TRUNKSNEO/HomeLab-PDU-V1/Images/10in-Dual/10in-Dual-B.png

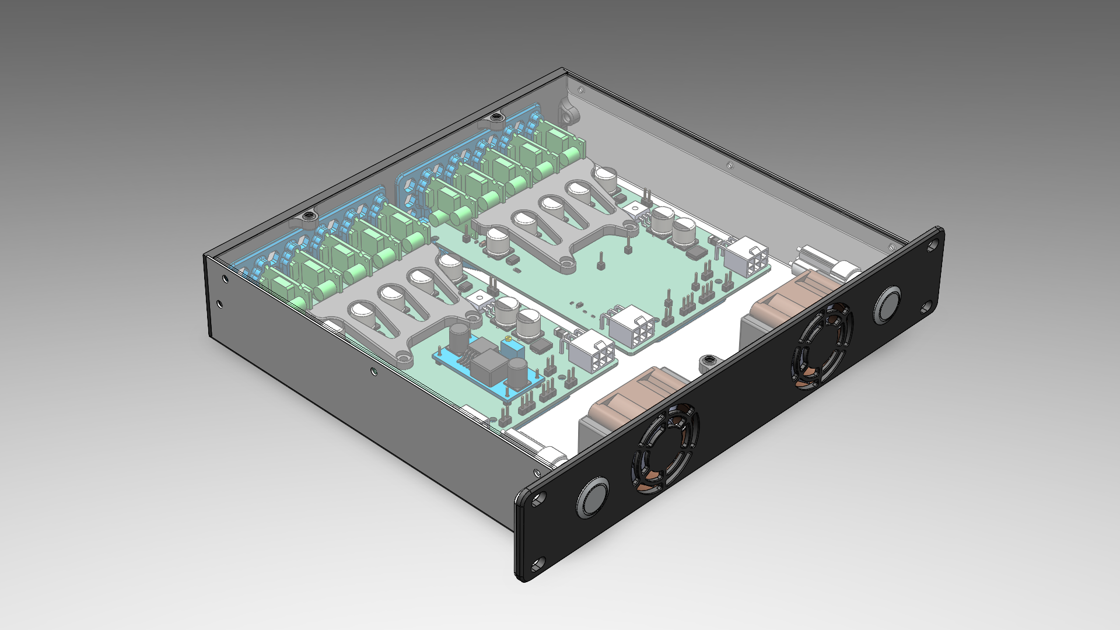
Images/10in-Dual/10in-Dual-B.png
