TRUNKSNEO/HomeLab-PDU-V1/Images/10in-Single/10in-Single-B.png

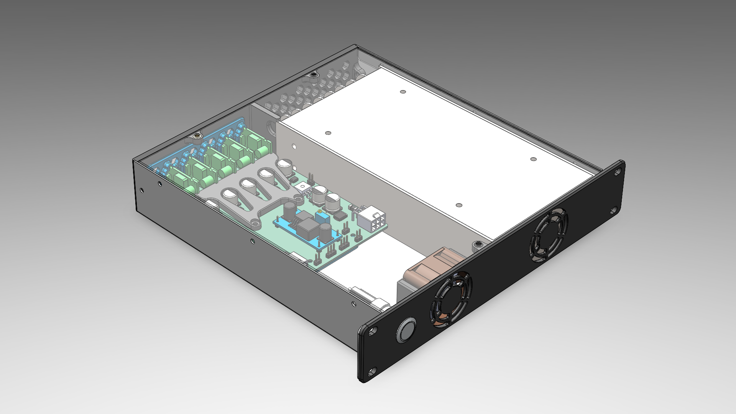
Images/10in-Single/10in-Single-B.png
