TRUNKSNEO/HomeLab-PDU-V1/Images/10in_3D_Modular/10in_3D_Modular-C.png

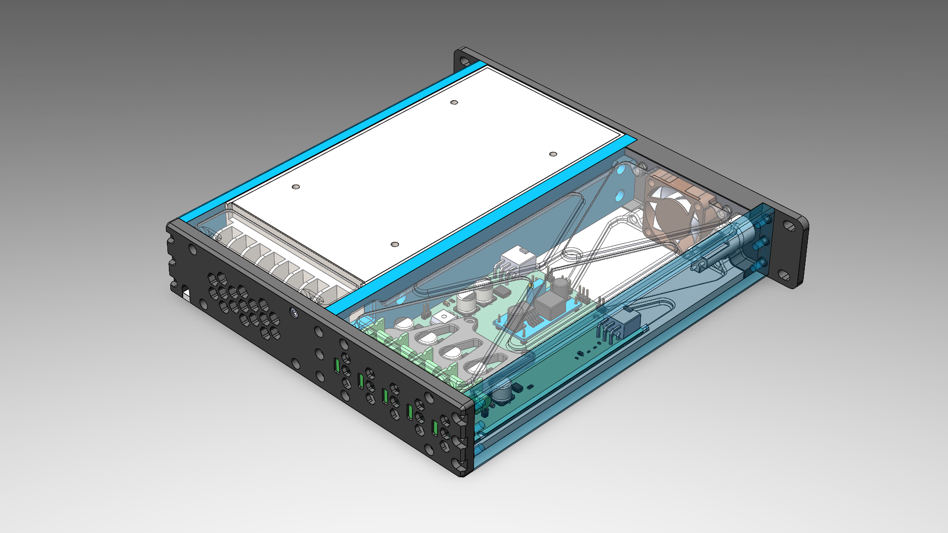
Images/10in_3D_Modular/10in_3D_Modular-C.png
