TRUNKSNEO/HomeLab-PDU-V1/Images/10in_3D_Unibody/10in_3D_Unibody-A.png

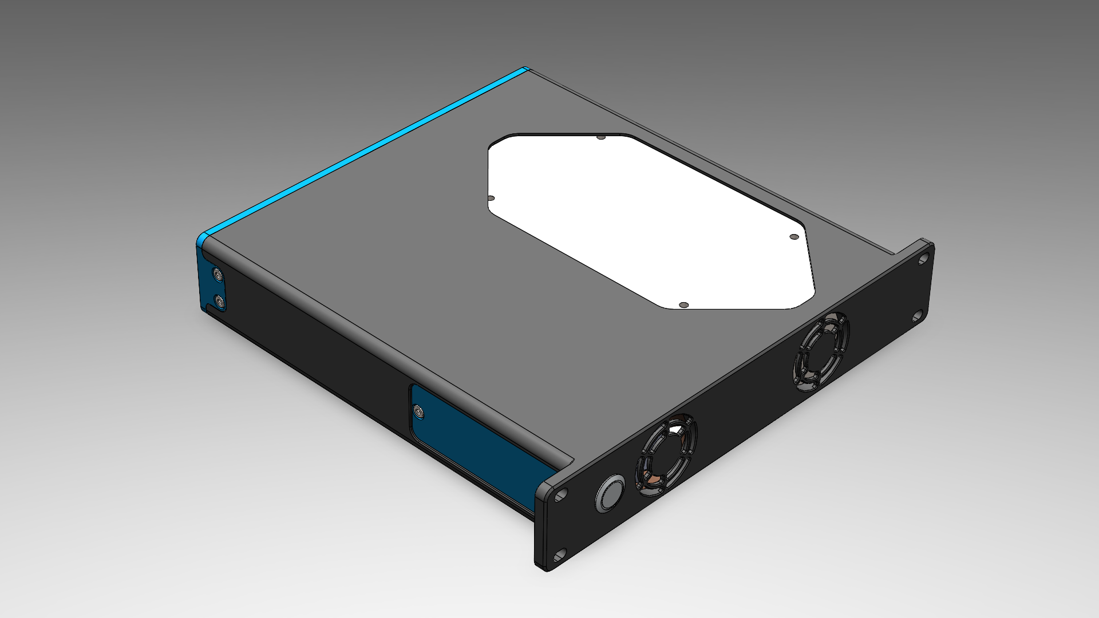
Images/10in_3D_Unibody/10in_3D_Unibody-A.png
