TRUNKSNEO/HomeLab-PDU-V1/Images/19in-Dual/19in-Dual-A.png

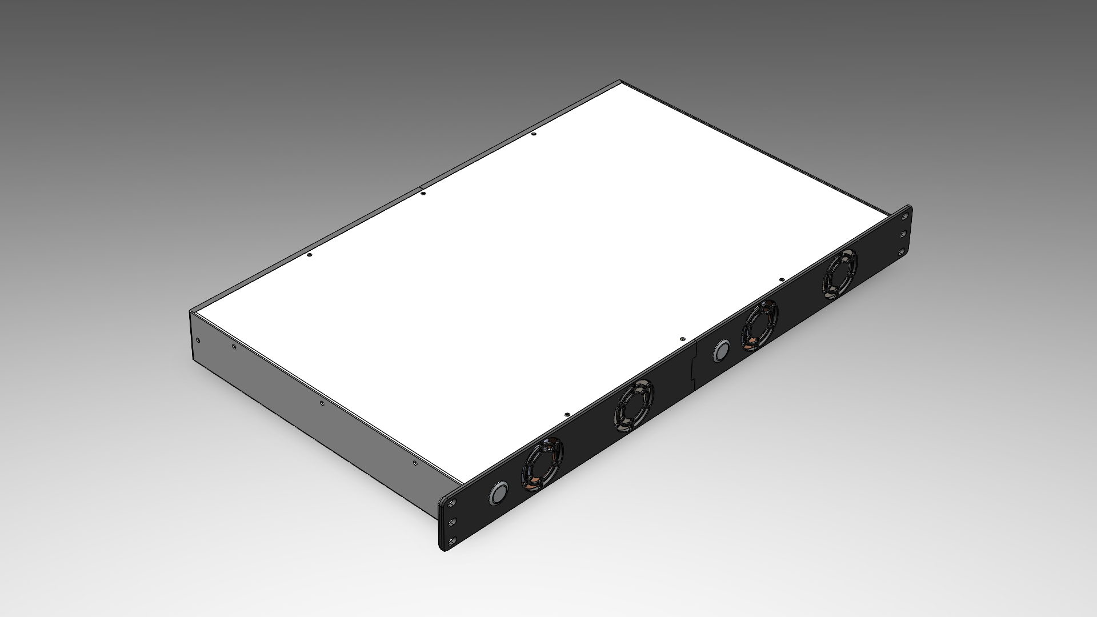
Images/19in-Dual/19in-Dual-A.png
