TRUNKSNEO/HomeLab-PDU-V1/Images/19in-SBS/19in-SBS-C.png

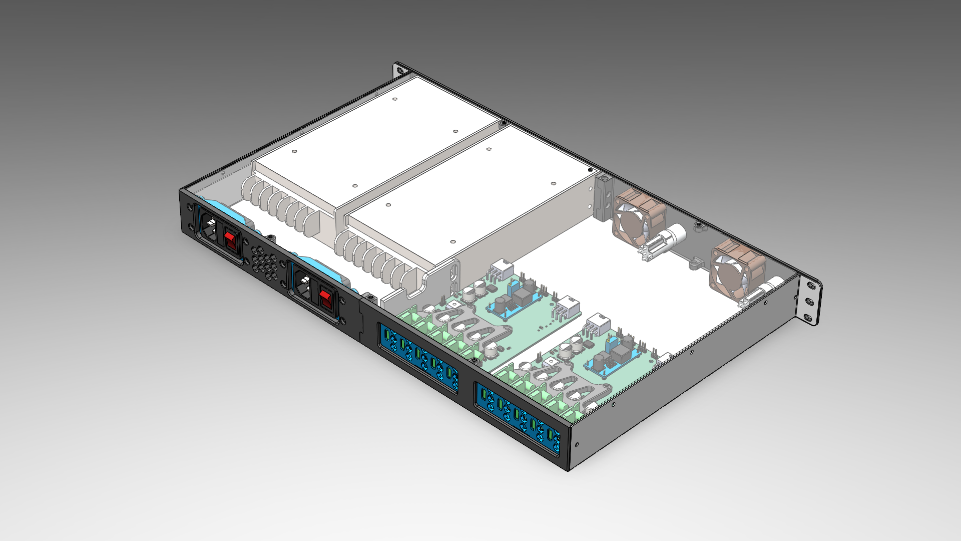
Images/19in-SBS/19in-SBS-C.png
