TRUNKSNEO/HomeLab-PDU-V1/Images/19in-Single/19in-Single-B.png

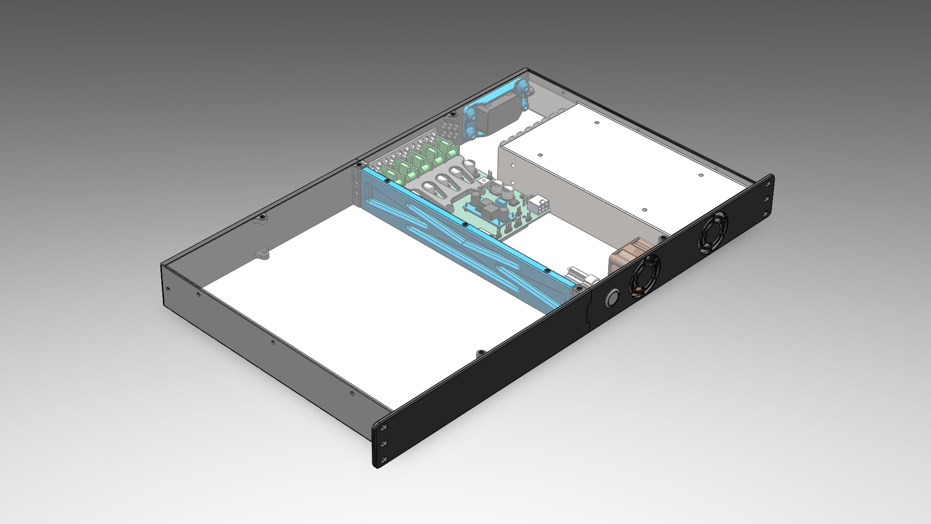
Images/19in-Single/19in-Single-B.png
