TRUNKSNEO/HomeLab-PDU-V1/Images/General/10in-Uni-Exp.png

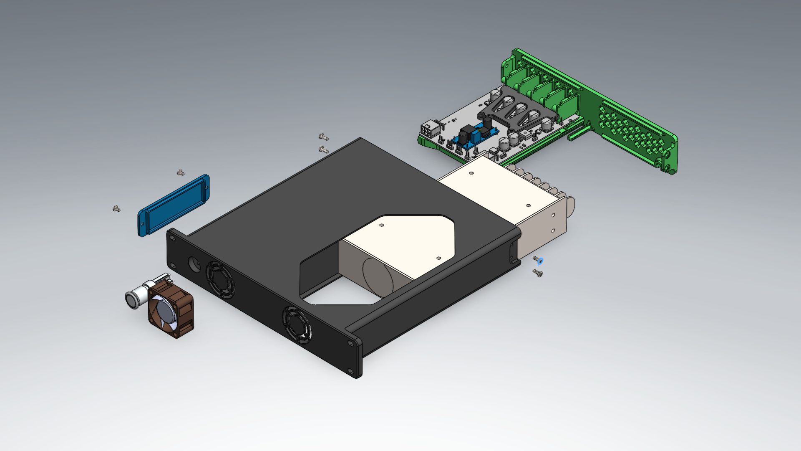
Images/General/10in-Uni-Exp.png
