TRUNKSNEO/HomeLab-PDU-V1/Images/General/19in-F+R.png

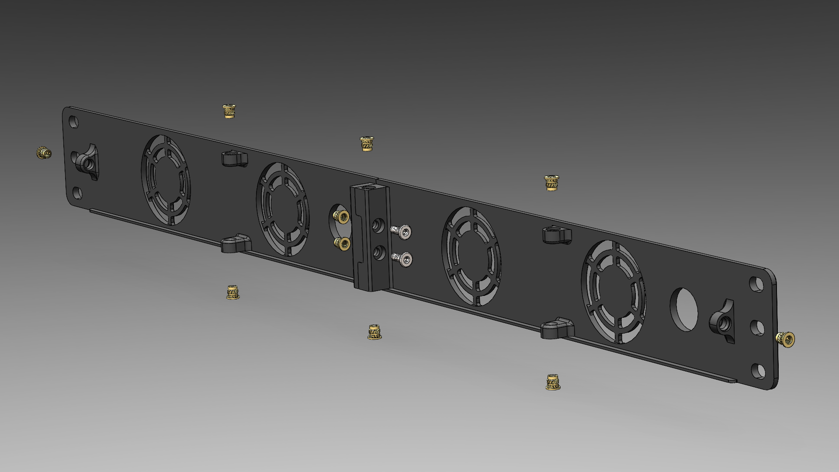
Images/General/19in-F+R.png
