TRUNKSNEO/HomeLab-PDU-V1/Images/General/LM2596S.png

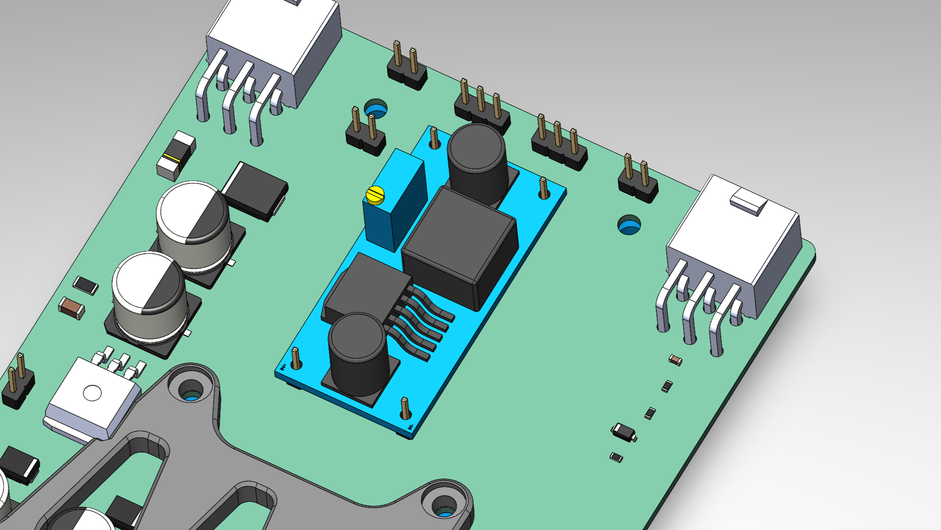
Images/General/LM2596S.png
