TRUNKSNEO/HomeLab-PDU-V1/Images/General/M3-Insert.png

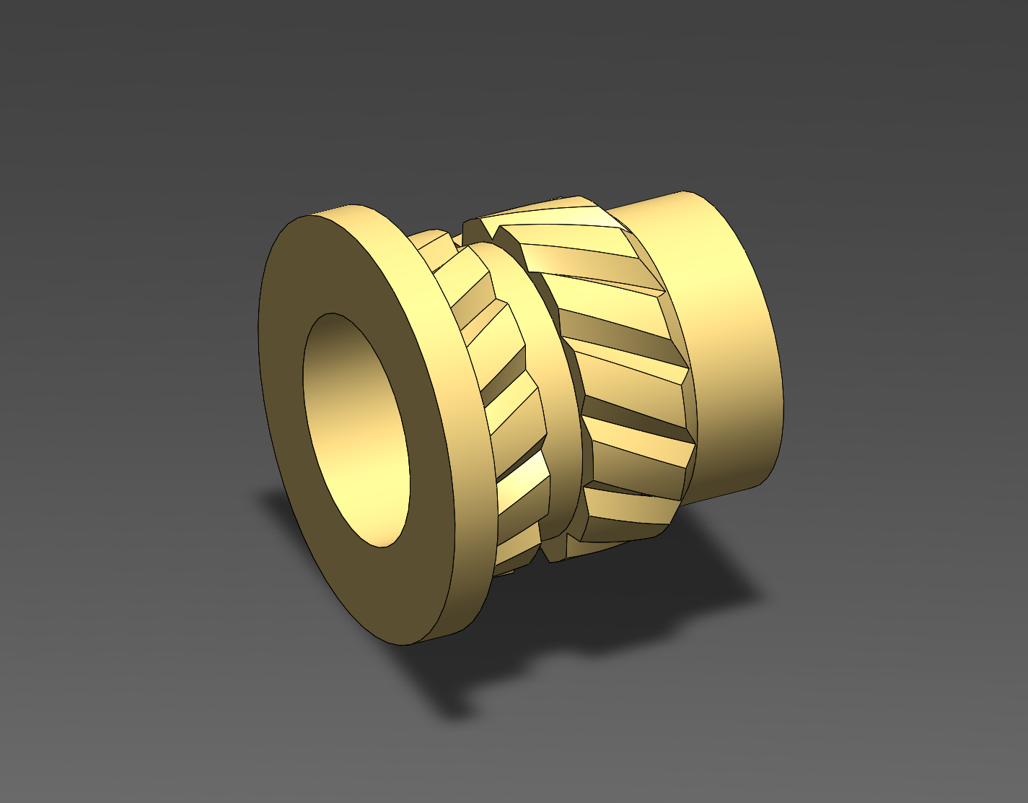
Images/General/M3-Insert.png
