TRUNKSNEO/HomeLab-PDU-V1/Images/General/MP1584EN.png

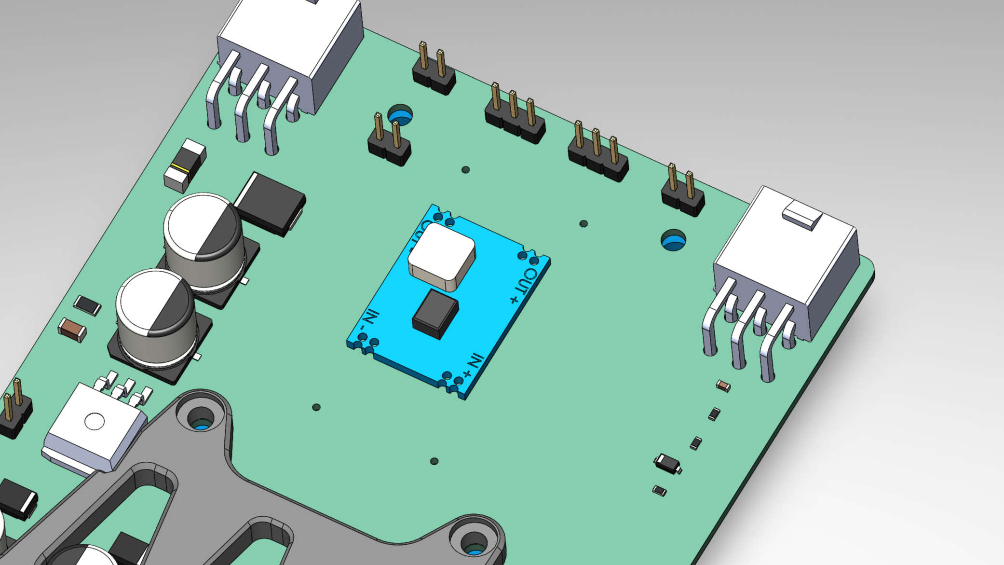
Images/General/MP1584EN.png
