TRUNKSNEO/HomeLab-PDU-V1/Images/General/Stacked.png

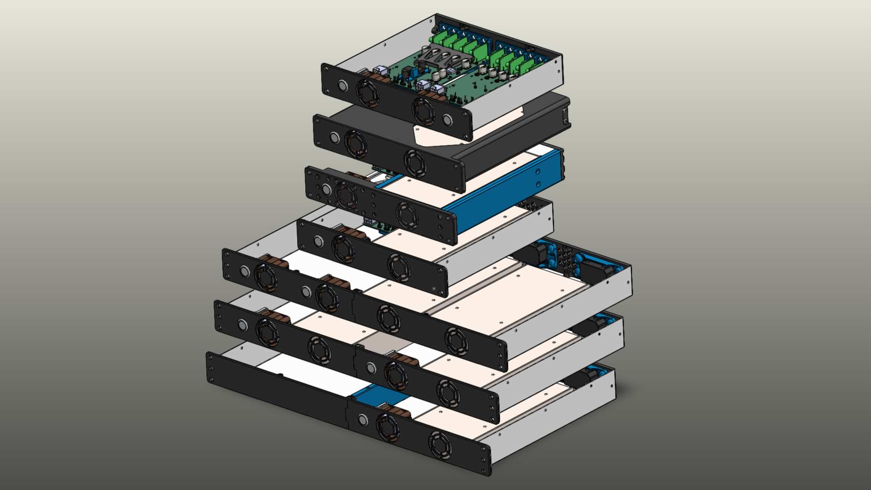
Images/General/Stacked.png
