TRUNKSNEO/HomeLab-PDU-V1/IMG/Drawings/Bolt-CapHead.png

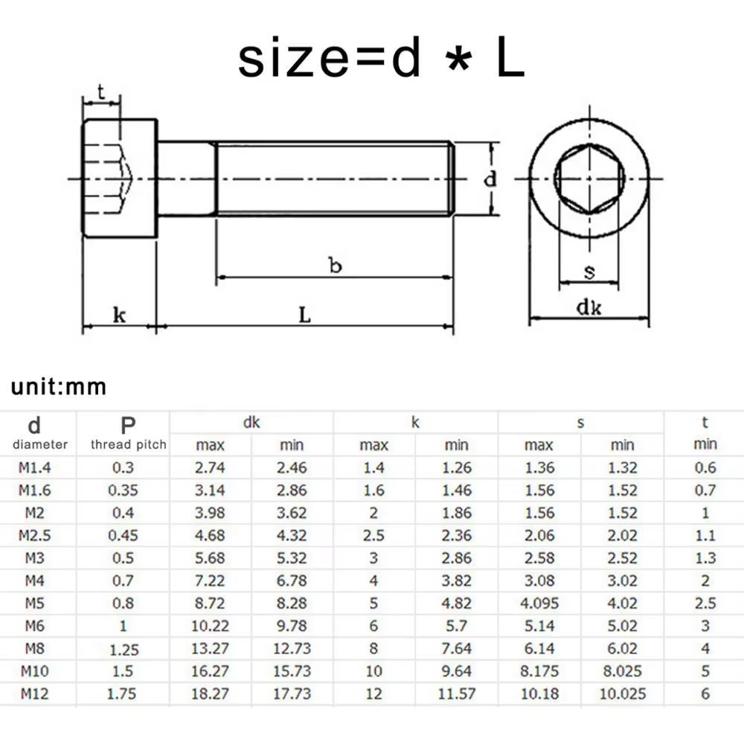
IMG/Drawings/Bolt-CapHead.png
