TRUNKSNEO/HomeLab-PDU-V1/IMG/Drawings/Bolt-LowProfile.png

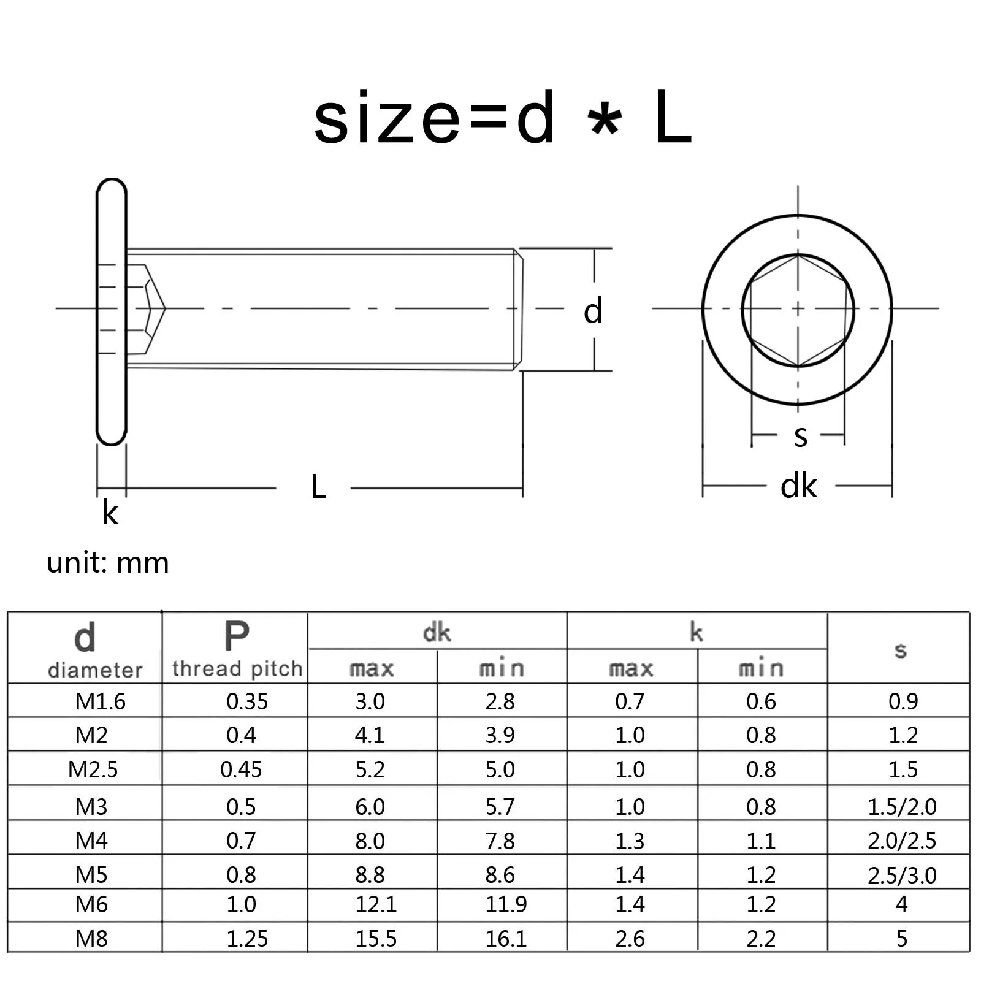
IMG/Drawings/Bolt-LowProfile.png
