TRUNKSNEO/HomeLab-PDU-V1/ASSEMBLY/CAD/19in_Dual_SBS/19in_Dual_SBS-Front_1.STL

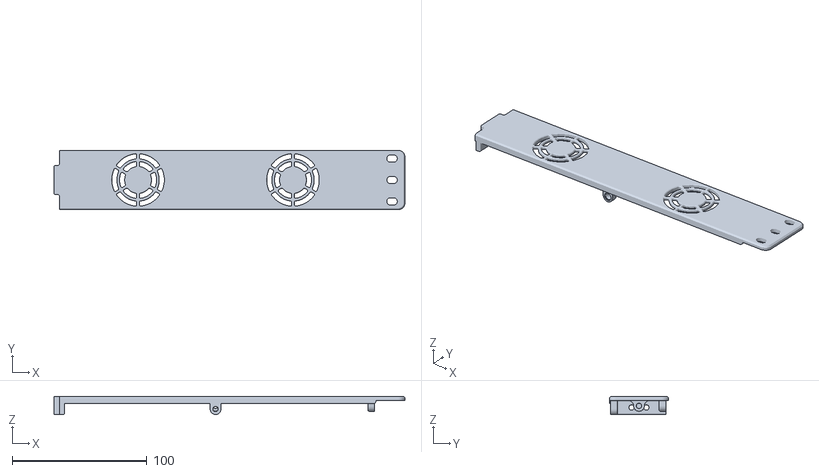
[picture p40: CAD file, 2026-04-01]
ASSEMBLY/CAD/19in_Dual_SBS/19in_Dual_SBS-Front_1.STL
260.5 x 44.0 x 13.4
