TRUNKSNEO/HomeLab-PDU-V1/ASSEMBLY/CAD/19in_Single/19in_Single-Front_2.stl

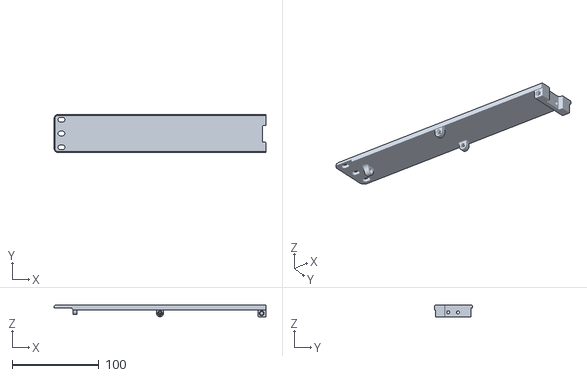
[picture p41: CAD file, 2026-04-01]
ASSEMBLY/CAD/19in_Single/19in_Single-Front_2.stl
244.1 x 44.0 x 13.4
