TRUNKSNEO/HomeLab-PDU-V1/ASSEMBLY/CAD/Blanks/IEC_Bracket.STEP

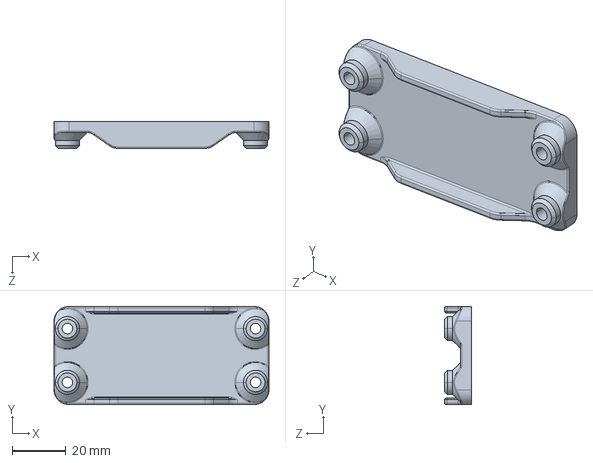
[picture p42: CAD file, 2026-04-01]
ASSEMBLY/CAD/Blanks/IEC_Bracket.STEP
80.0 x 36.5 x 10.0 mm
