TRUNKSNEO/HomeLab-PDU-V1/ASSEMBLY/CAD/Universal/Reinforcement_Bracket.STL

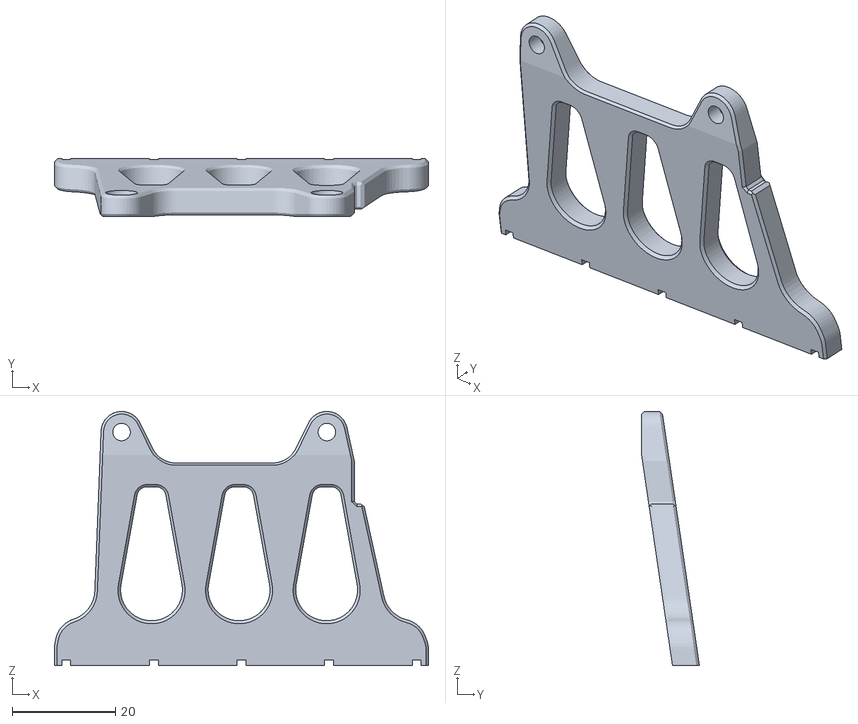
[picture p43: CAD file, 2026-04-04]
ASSEMBLY/CAD/Universal/Reinforcement_Bracket.STL
72.6 x 11.2 x 49.3
