TRUNKSNEO/HomeLab-PDU-V1/ASSEMBLY/CAD/10in_3D_Modular/10in_3D-Left.stl

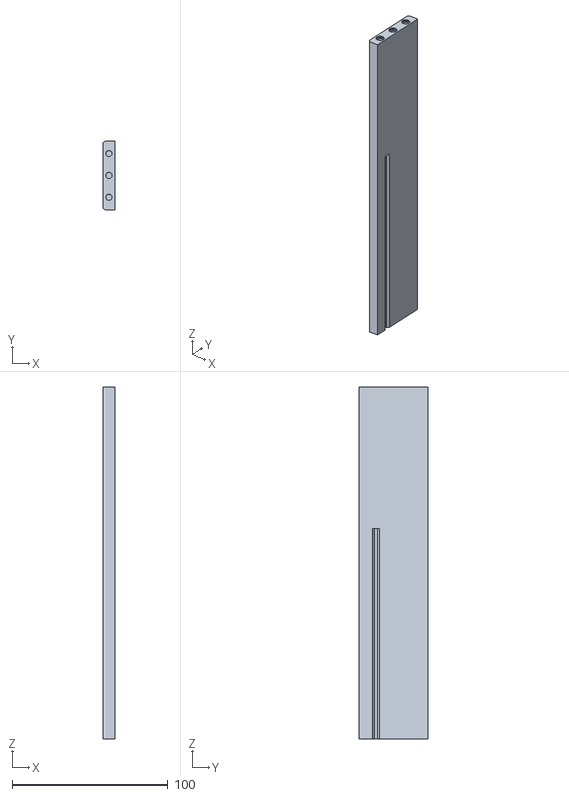
[picture p44: CAD file, 2026-04-01]
ASSEMBLY/CAD/10in_3D_Modular/10in_3D-Left.stl
8.00 x 44.0 x 226.0
