TRUNKSNEO/HomeLab-PDU-V1/ASSEMBLY/CAD/10in_3D_Unibody/10in_Uni-Tray.STEP

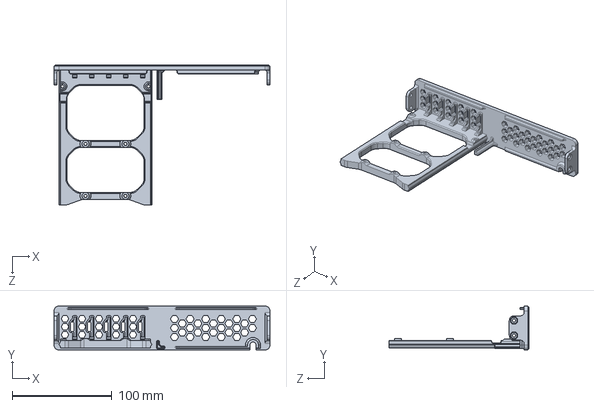
[picture p45: CAD file, 2026-04-07]
ASSEMBLY/CAD/10in_3D_Unibody/10in_Uni-Tray.STEP
216.0 x 44.0 x 140.0 mm
