TRUNKSNEO/HomeLab-PDU-V1/ASSEMBLY/CAD/10in_Dual/10in_Dual-Tray.stp

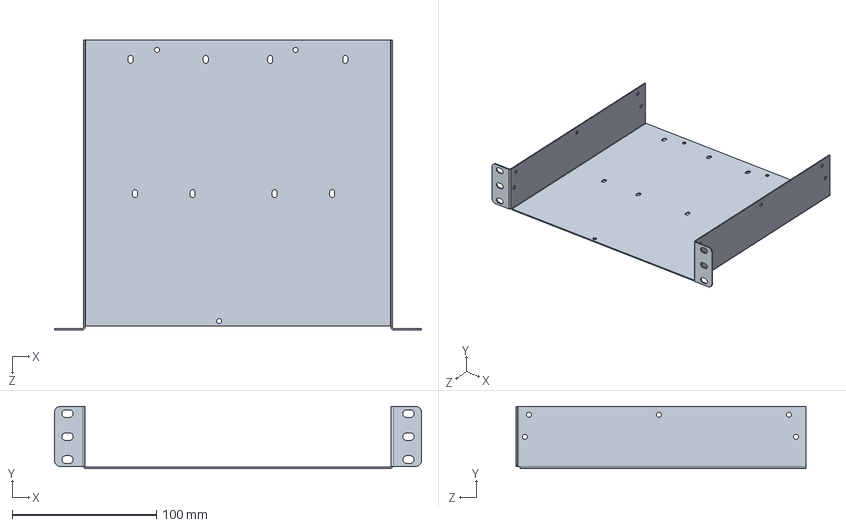
[picture p46: CAD file, 2026-04-01]
ASSEMBLY/CAD/10in_Dual/10in_Dual-Tray.stp
254.0 x 43.0 x 200.5 mm
