TRUNKSNEO/HomeLab-PDU-V1/ASSEMBLY/CAD/10in_Single/10in_Single-Front.stl

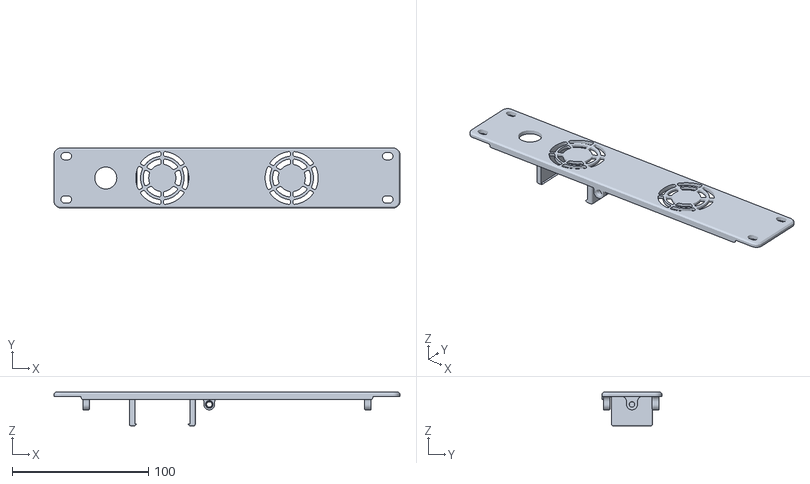
[picture p47: CAD file, 2026-04-01]
ASSEMBLY/CAD/10in_Single/10in_Single-Front.stl
254.0 x 44.0 x 24.7
