TRUNKSNEO/HomeLab-PDU-V1/ASSEMBLY/CAD/Blanks/10in_Dual-Back-BLANK.STEP

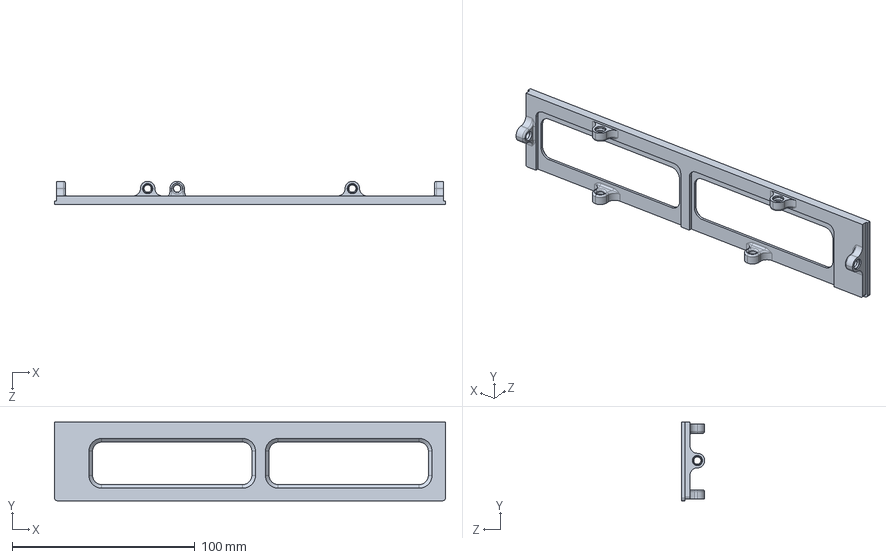
[picture p48: CAD file, 2026-04-01]
ASSEMBLY/CAD/Blanks/10in_Dual-Back-BLANK.STEP
214.0 x 43.0 x 12.8 mm
