TRUNKSNEO/HomeLab-PDU-V1/ASSEMBLY/CAD/10in_3D_Modular/10in_3D-Back.stl

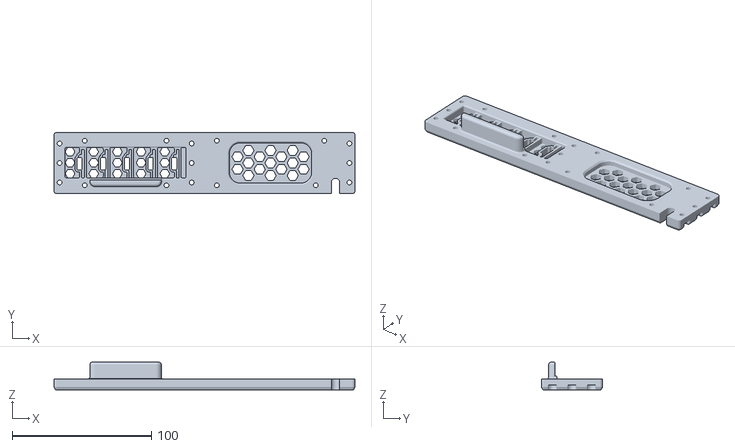
[picture p49: CAD file, 2026-04-01]
ASSEMBLY/CAD/10in_3D_Modular/10in_3D-Back.stl
216.0 x 44.0 x 20.0
