TRUNKSNEO/HomeLab-PDU-V1/ASSEMBLY/CAD/10in_Single/10in_Single-Rear.stl

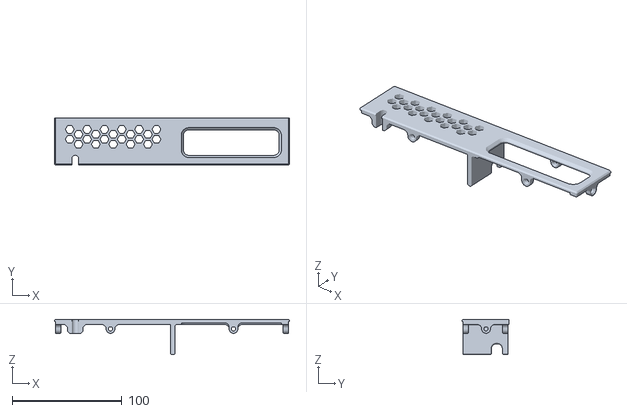
[picture p50: CAD file, 2026-04-01]
ASSEMBLY/CAD/10in_Single/10in_Single-Rear.stl
214.0 x 43.0 x 32.3
