TRUNKSNEO/HomeLab-PDU-V1/ASSEMBLY/CAD/19in_Dual/19in_Dual-Rear_1.stl

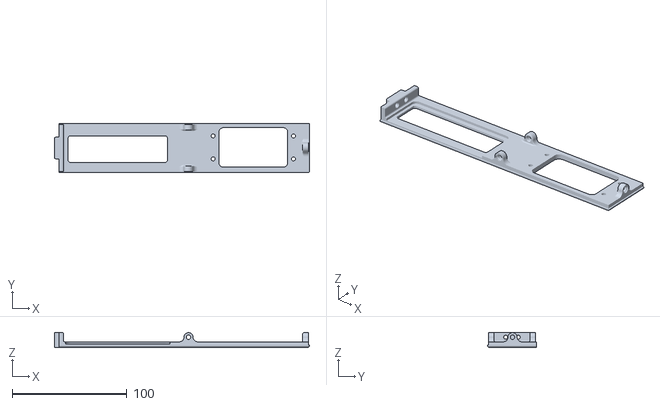
[picture p51: CAD file, 2026-04-01]
ASSEMBLY/CAD/19in_Dual/19in_Dual-Rear_1.stl
222.4 x 43.0 x 12.8
