TRUNKSNEO/HomeLab-PDU-V1/ASSEMBLY/CAD/19in_Dual_SBS/19in_Dual_SBS-Tray.stp

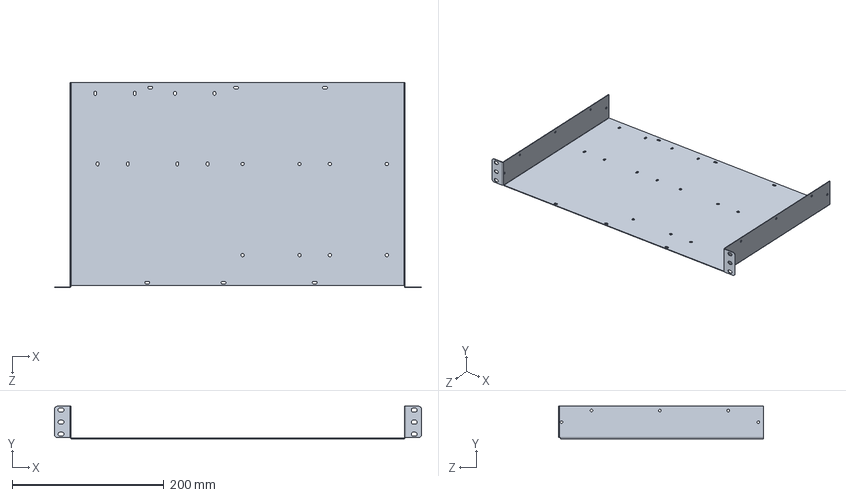
[picture p52: CAD file, 2026-04-01]
ASSEMBLY/CAD/19in_Dual_SBS/19in_Dual_SBS-Tray.stp
483.2 x 43.0 x 270.0 mm
