TRUNKSNEO/HomeLab-PDU-V1/ASSEMBLY/CAD/19in_Single/19in_Single-Rear_2.stl

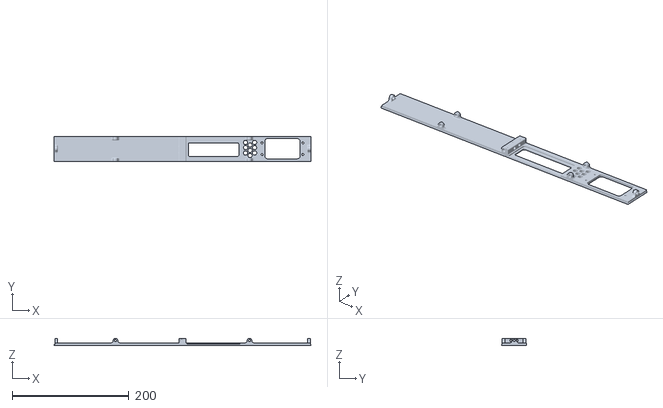
[picture p53: CAD file, 2026-04-01]
ASSEMBLY/CAD/19in_Single/19in_Single-Rear_2.stl
441.0 x 43.0 x 12.8
