TRUNKSNEO/HomeLab-PDU-V1/ASSEMBLY/CAD/10in_3D_Modular/10in_3D-Middle.stl

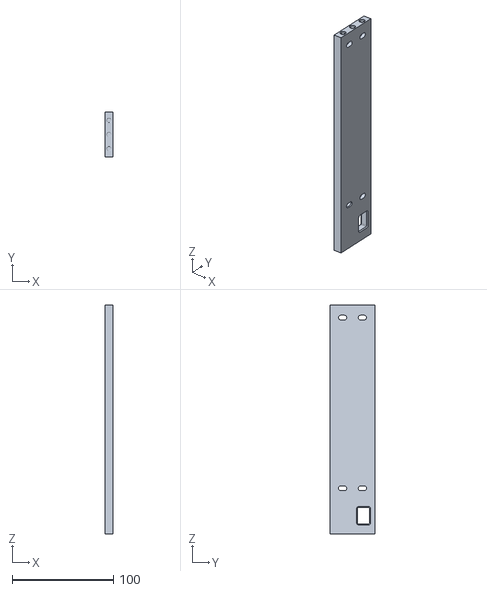
[picture p54: CAD file, 2026-04-01]
ASSEMBLY/CAD/10in_3D_Modular/10in_3D-Middle.stl
8.00 x 44.0 x 226.0
