TRUNKSNEO/HomeLab-PDU-V1/ASSEMBLY/CAD/10in_Dual/10in_Dual-Front.stl

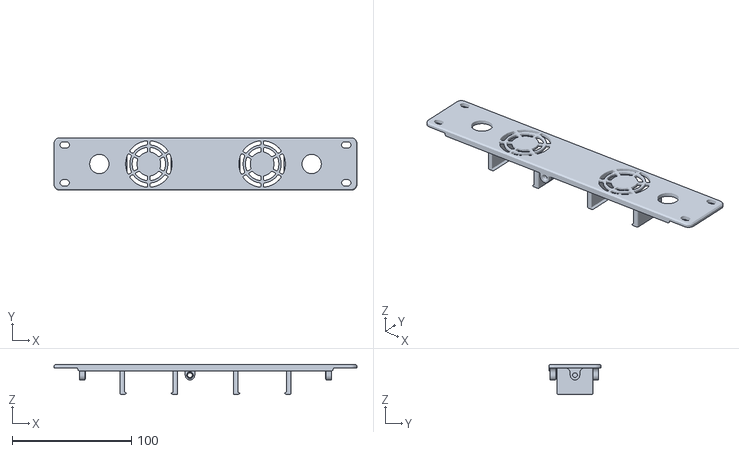
[picture p55: CAD file, 2026-04-01]
ASSEMBLY/CAD/10in_Dual/10in_Dual-Front.stl
254.0 x 44.0 x 25.2
