TRUNKSNEO/HomeLab-PDU-V1/ASSEMBLY/CAD/19in_Single/19in_Single-Internal.STL

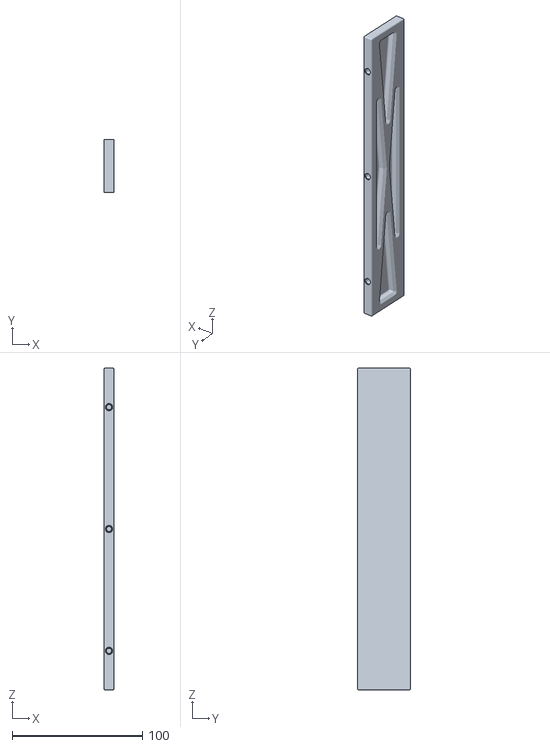
[picture p56: CAD file, 2026-04-01]
ASSEMBLY/CAD/19in_Single/19in_Single-Internal.STL
8.00 x 41.0 x 246.8
