TRUNKSNEO/HomeLab-PDU-V1/ASSEMBLY/CAD/10in_3D_Modular/10in_3D-Bottom_2.stl

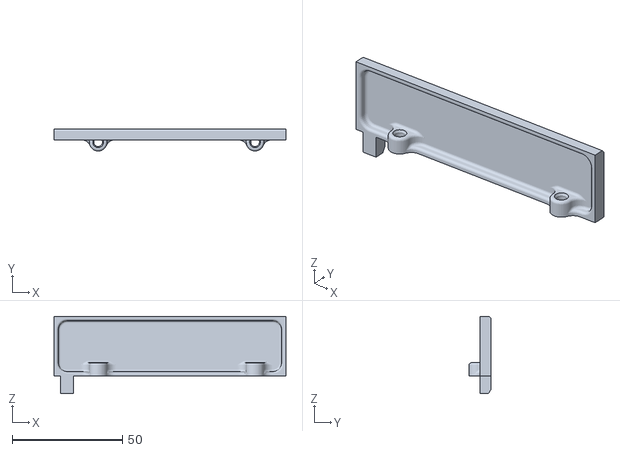
[picture p57: CAD file, 2026-04-01]
ASSEMBLY/CAD/10in_3D_Modular/10in_3D-Bottom_2.stl
105.0 x 10.0 x 35.0
