TRUNKSNEO/HomeLab-PDU-V1/ASSEMBLY/CAD/10in_Dual/10in_Dual-Lid.stp

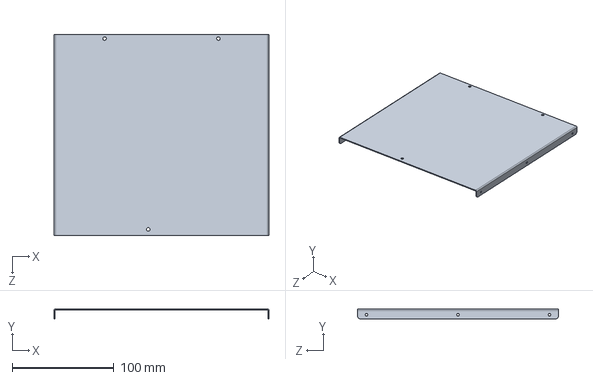
[picture p58: CAD file, 2026-04-01]
ASSEMBLY/CAD/10in_Dual/10in_Dual-Lid.stp
211.5 x 10.0 x 197.5 mm
