TRUNKSNEO/HomeLab-PDU-V1/ASSEMBLY/CAD/10in_3D_Modular/10in_3D-Front.stl

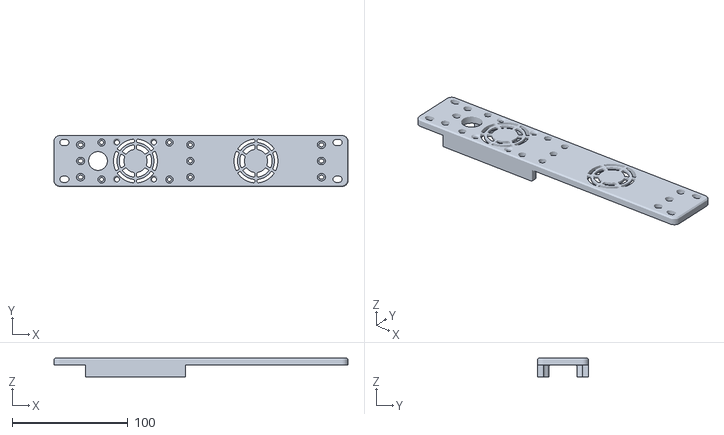
[picture p59: CAD file, 2026-04-01]
ASSEMBLY/CAD/10in_3D_Modular/10in_3D-Front.stl
254.0 x 44.0 x 16.0
