TRUNKSNEO/HomeLab-PDU-V1/ASSEMBLY/CAD/19in_Dual_SBS/19in_Dual_SBS-Front_2.STL

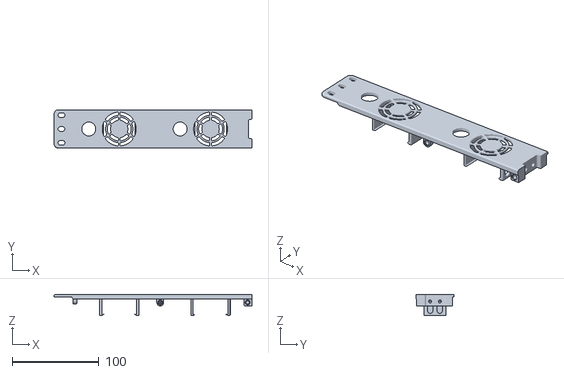
[picture p60: CAD file, 2026-04-01]
ASSEMBLY/CAD/19in_Dual_SBS/19in_Dual_SBS-Front_2.STL
227.6 x 44.0 x 24.7
