TRUNKSNEO/HomeLab-PDU-V1/ASSEMBLY/DRAWINGS/Electrial/Buck_Board.png

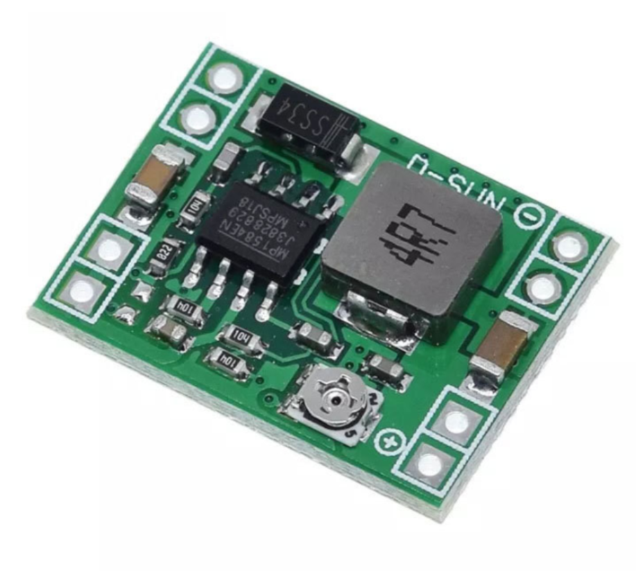
ASSEMBLY/DRAWINGS/Electrial/Buck_Board.png
