TRUNKSNEO/HomeLab-PDU-V1/ASSEMBLY/DRAWINGS/Electrial/Heatsink.png

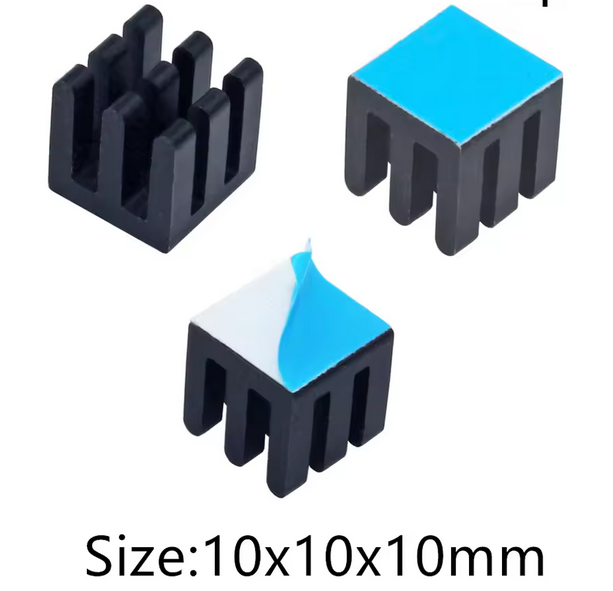
ASSEMBLY/DRAWINGS/Electrial/Heatsink.png
