TRUNKSNEO/HomeLab-PDU-V1/Images/General/PCB-Assembly-Bracket.png

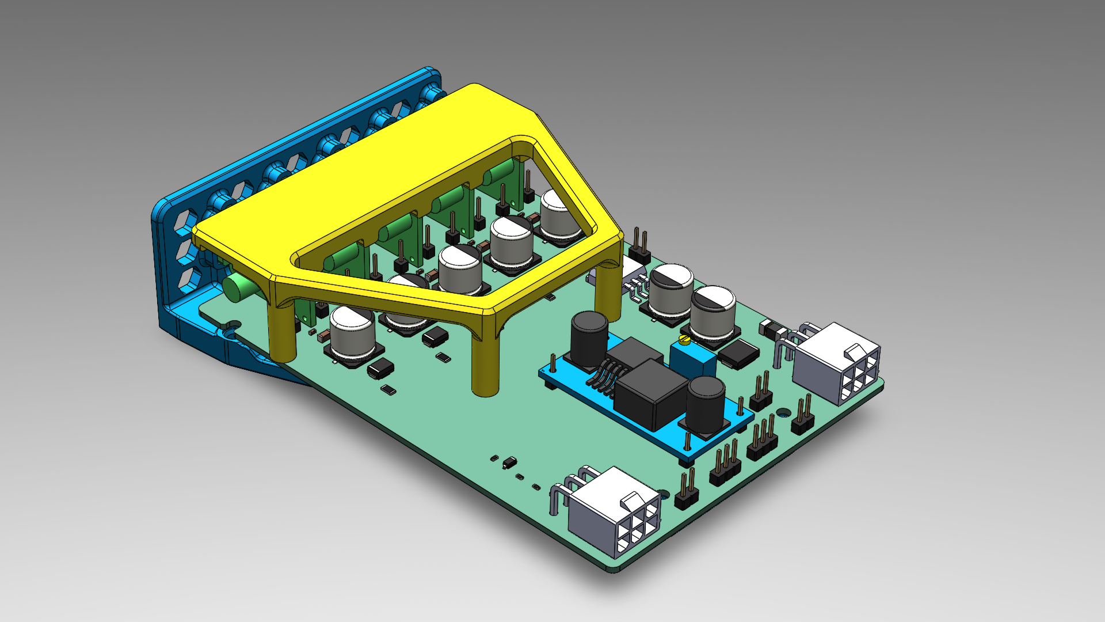
Images/General/PCB-Assembly-Bracket.png
