TRUNKSNEO/HomeLab-PDU-V1/Images/General/PCB-Assembly-Reinforcement.png

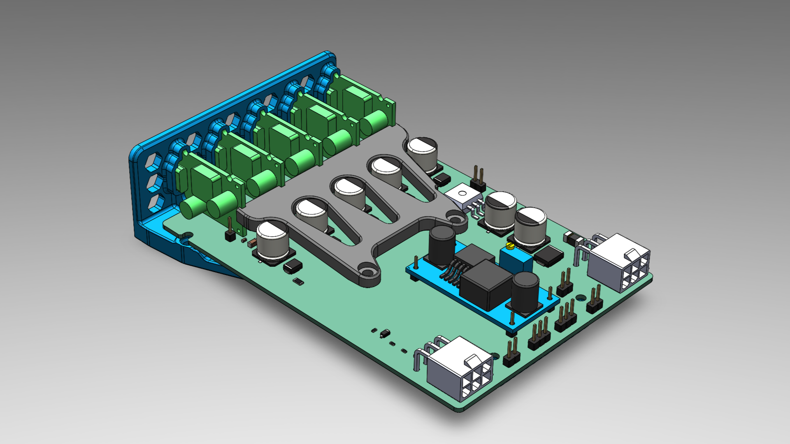
Images/General/PCB-Assembly-Reinforcement.png
