TRUNKSNEO/HomeLab-PDU-V1/Images/General/PCB-Assembly.png

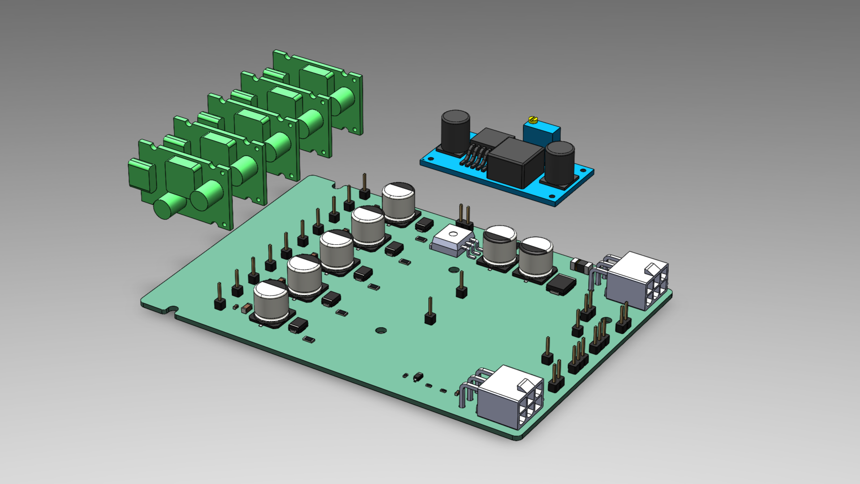
Images/General/PCB-Assembly.png
