TRUNKSNEO/HomeLab-PDU-V1/Images/General/PCB-SubAssembly.png

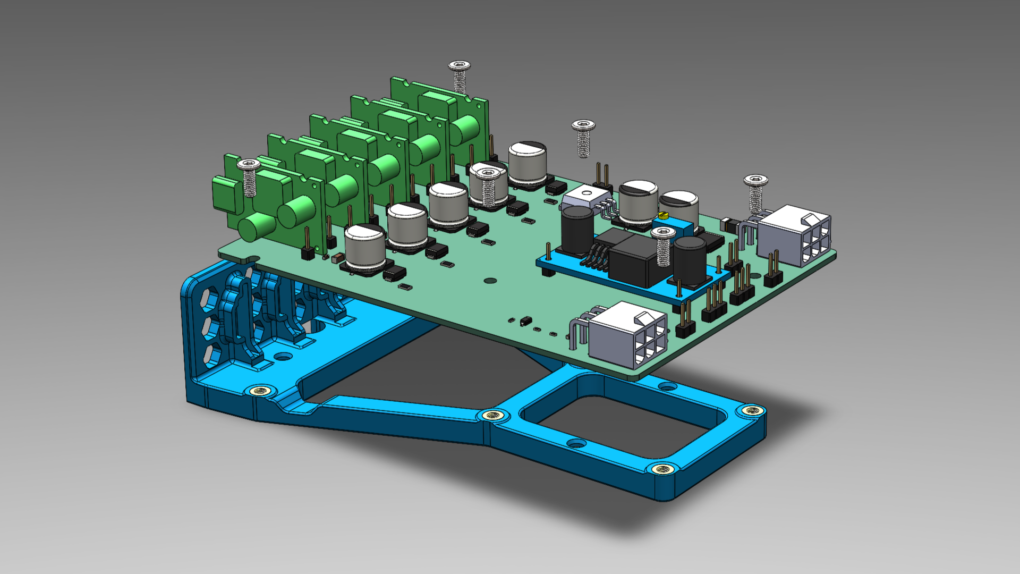
Images/General/PCB-SubAssembly.png
