TRUNKSNEO/HomeLab-PDU-V1/Images/General/PIC-Front.jpg

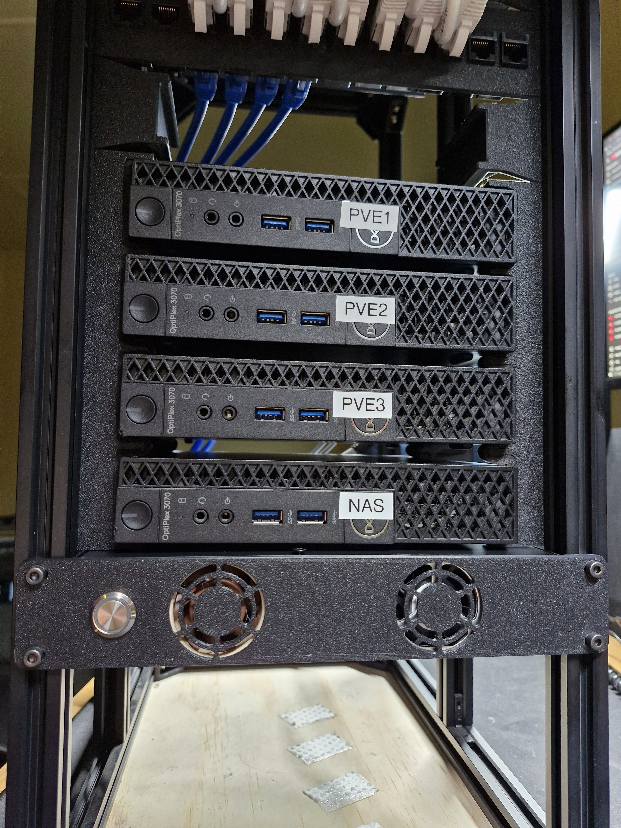
Images/General/PIC-Front.jpg
