TRUNKSNEO/HomeLab-PDU-V1/Images/General/PIC-Rear.jpg

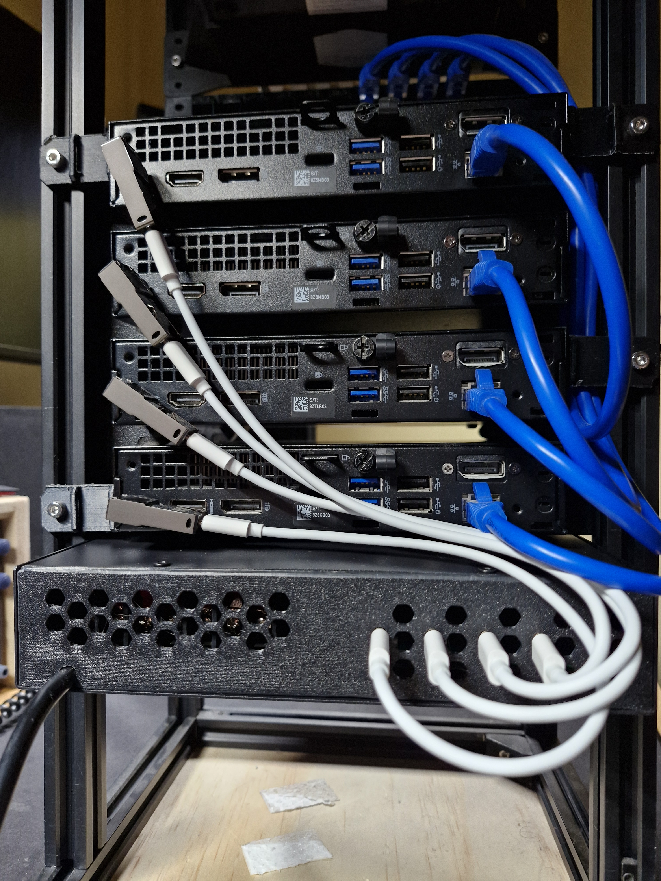
Images/General/PIC-Rear.jpg
